MatiMcFly/DIY_ToF/docs/documentation/acronympage.tex

\section*{Abkürzungsverzeichnis}
\vspace{-25pt}
\printglossary[type=\acronymtype,title={}]

\pagebreak
