MatiMcFly/DIY_ToF/docs/presentation/english/conclusion.tex

\begin{frame}{Outlook}
    \begin{itemize}
        \item Optimize the optics, try other focal lengths
        \item Minimize jitter (higher clock or external clock)
        \item Switch GPIOs faster
        \item Optical receive path
              \begin{itemize}
                  \item Different amplifications TIA
                  \item Different switching thresholds for comparator
              \end{itemize}
        \item Optical transmission path: try higher transmission power
        \item Analysis of optical results: why two clusters?
        \item Mechanical test setup for mirror
    \end{itemize}
\end{frame}

\begin{frame}{Lessons Learned}
    \begin{itemize}
        \item Overall very satisfied
        \item Learned a lot of new things
        \item Unfortunately, a little short of time
        \item Time resolution less of a problem than the amount of light received
        \item[$\Rightarrow$] Invest more time in optics and optoelectronics
        \item[$\Rightarrow$] Easy to get an application running with a TDC7200
    \end{itemize}
\end{frame}
