MatiMcFly/DIY_ToF/docs/presentation/english/objective.tex

\begin{frame}{Setting}
    \begin{itemize}
        \item Part of a CAS -- Certificate Advanced Studies
              \begin{itemize}
                  \item CAS are post graduate studies (after bachelor/master)
                  \item CAS typically take 15 ECTS / 1 semester
                  \item Part time, e.g., Fri + Sat
              \end{itemize}
        \item<2-> CAS Sensors and Sensor Signal Conditioning \cite{ost2025casssc}
        \item<2-> As part of it: 5 week project work
    \end{itemize}
\end{frame}

\begin{frame}{Objective}
    \begin{itemize}
        \item Get familiar with TDCs (Time to Digital Converters)
              \begin{itemize}
                  \item Find out how much effort it takes to get TDC application running
              \end{itemize}
        \item<2-> Develop optical ToF demonstrator for distance measurement
              \begin{itemize}
                  \item Custom PCB with 2x TDC7200
              \end{itemize}
        \item<3-> First step: Electrical measurements (cable lengths)
        \item<3-> Second step: Optical measurements
              \begin{itemize}
                  \item Distance: 10 m
                  \item Resolution: 30 cm
              \end{itemize}
        \item<4->[$\Rightarrow$] Focused on getting practical experience; not very scientific
    \end{itemize}
\end{frame}

\begin{frame}{GitHub}
    \begin{itemize}
        \item I'm trying not to get too technical
        \item Full project (HW + FW) is available on GitHub: \url{https://github.com/MatiMcFly/DIY_ToF}
        \item<2-> Documentation English: \url{https://github.com/MatiMcFly/DIY_ToF/blob/main/docs/documentation/english/documentation.pdf}
              \begin{itemize}
                  \item Automatically translated with DeepL
              \end{itemize}
        \item<2-> Original German version: \url{https://github.com/MatiMcFly/DIY_ToF/blob/main/docs/documentation/documentation.pdf}
    \end{itemize}
\end{frame}
