MatiMcFly/DIY_ToF/docs/presentation/english/realization.tex

\begin{frame}{TDC}
    \begin{itemize}
        \item TDC7200 from TI \cite{ti2025tdc7200}
              \begin{itemize}
                  \item Resolution: 55~ps
                  \item Range 1: 12~ns \dots 500~ns
                  \item Range 2: 250~ns \dots 8~ms
                  \item Digital interface: SPI
              \end{itemize}
    \end{itemize}

    \begin{columns}
        \column{0.3\textwidth}
        \begin{figure}
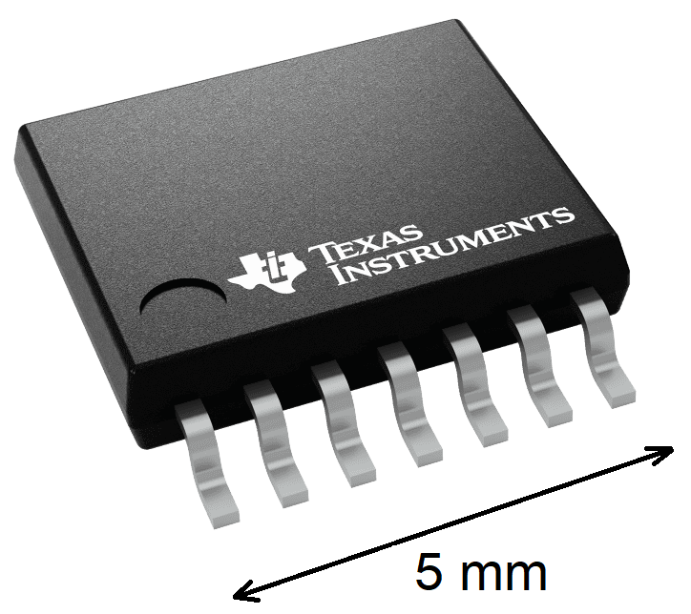
[picture p36: docs/presentation/english/graphics/tdc7200.png]
            
        \end{figure}

        \column{0.7\textwidth}
        \begin{figure}
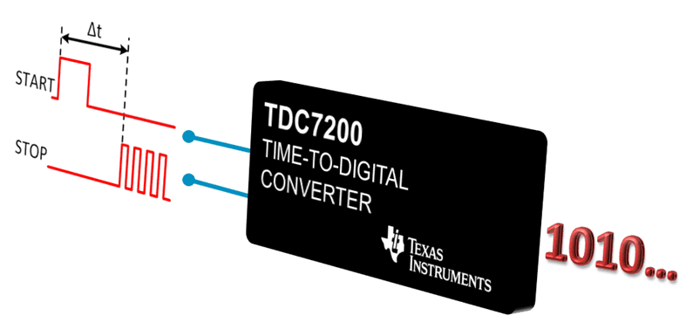
[picture p37: docs/presentation/english/graphics/tdc7200_diagram.png]
            
        \end{figure}
    \end{columns}
\end{frame}

\begin{frame}{Block diagram}
    \begin{figure}
        
    \end{figure}

    \onslide<2->{
        \begin{tikzpicture}[remember picture, overlay]
            \node at ([xshift=8.3cm, yshift=-2.6cm]current page.north west) {
                \includesvg[width=1cm]{../graphics/icon_electrical.svg}
            };
        \end{tikzpicture}

        \begin{tikzpicture}[remember picture, overlay]
            \node at ([xshift=7.9cm, yshift=-6.4cm]current page.north west) {
                \includesvg[width=1cm]{../graphics/icon_optical.svg}
            };
        \end{tikzpicture}
    }
\end{frame}

\begin{frame}{Concept: Optical Part}
    \begin{figure}
        
    \end{figure}
    \iconoptical
\end{frame}

\subsection{Circuits}

\begin{frame}{TDC Electrical}
    \begin{figure}
        
    \end{figure}
    \iconelectrical
\end{frame}

\begin{frame}{TDC Optical}
    \begin{figure}
        
    \end{figure}
    \iconoptical
\end{frame}

\begin{frame}{Laser Driver}
    \begin{figure}
        
    \end{figure}
    \iconoptical
\end{frame}

\begin{frame}{Photo Receiver}
    \begin{figure}
        
    \end{figure}
    \iconoptical
\end{frame}

\begin{frame}{3D View}
    \begin{figure}
        
    \end{figure}
\end{frame}

\begin{frame}{Demonstrator}
    \begin{figure}
        
    \end{figure}
\end{frame}

\subsection{Firmware}

\begin{frame}{Firmware block diagram}
    \begin{figure}
        
    \end{figure}
\end{frame}

\begin{frame}{Firmware example: configuration}
    \only<1>{\codehighlight{C}{1}{99}{../sourcecode/tdc_example_config.c}}
    \only<2>{\codehighlight{C}{1}{5}{../sourcecode/tdc_example_config.c}}
    \only<3>{\codehighlight{C}{7}{13}{../sourcecode/tdc_example_config.c}}
\end{frame}

\begin{frame}{Firmware example: Measurement}
    \only<1>{\codehighlight{C}{1}{99}{../sourcecode/tdc_example_measure.c}}
    \only<2>{\codehighlight{C}{4}{4}{../sourcecode/tdc_example_measure.c}}
    \only<3>{\codehighlight{C}{6}{8}{../sourcecode/tdc_example_measure.c}}
    \only<4>{\codehighlight{C}{10}{10}{../sourcecode/tdc_example_measure.c}}
    \only<5>{\codehighlight{C}{12}{12}{../sourcecode/tdc_example_measure.c}}
\end{frame}
