MatiMcFly/DIY_ToF/docs/presentation/english/tocframe.tex

\begin{frame}{Table of contents}
    \tableofcontents
\end{frame}
