MatiMcFly/DIY_ToF/docs/documentation/english/acronympage.tex

\section*{List of Acronyms}
\vspace{-25pt}
\printglossary[type=\acronymtype,title={}]

\pagebreak
