MatiMcFly/DIY_ToF/docs/documentation/english/appendix.tex

\subsection{Outline}\label{sec:outline}

\begin{figure}[H]
    \centering
    
    \caption{Outline}\label{fig:outline}
\end{figure}

\subsection{TDC Driver}\label{sec:tdc_driver}

The code in \ref{code:tdc_driver_header} and \ref{code:tdc_driver_source} shows the firmware driver developed in-house
for the \acrshort{tdc}.

\lstinputlisting[language={c}, label={code:tdc_driver_header}, caption={\acrshort{tdc} Driver (Header)}]{../../../firmware/Core/TDC/TDC.h}
\lstinputlisting[language={c}, label={code:tdc_driver_source}, caption={\acrshort{tdc} Driver (Source)}]{../../../firmware/Core/TDC/TDC.c}

\subsection{Python Scripts}\label{sec:python_scripts}

The Python script for calculating the arithmetic mean and the standard deviation, as well as for plotting the histogram
and the box plot, is shown in code \ref{code:python_analyze}.

\lstinputlisting[language={python}, label={code:python_analyze}, caption={Python Analysis}]{../../../utilities/analyze-tof.py}

The Python script for calculating the arithmetic mean and standard deviation and for plotting the values for several
\acrshort{tof} data sets is shown in code \ref{code:python_analyze_multi_tofs}.

\lstinputlisting[language={python}, label={code:python_analyze_multi_tofs}, caption={Python Analysis (Multi \acrshort{tof}s)}]{../../../utilities/analyze-tofs.py}

The Python script for plotting the values from several log files is shown in code \ref{code:python_analyze_multi_logs}.

\lstinputlisting[language={python}, label={code:python_analyze_multi_logs}, caption={Python Analysis (Multi Logs)}]{../../../utilities/analyze-tofs-multi-logs.py}

The Python script for live plotting of \acrshort{tof} values is shown in code \ref{code:python_live_plot}. This will be
used during the presentation for demonstration purposes.

\lstinputlisting[language={python}, label={code:python_live_plot}, caption={Python Live Plot}]{../../../utilities/live-plot.py}

\pagebreak

\begin{landscape}
    \subsection{Schema}\label{sec:schematic_apdx}

    \global\pdfpageattr\expandafter{\the\pdfpageattr/Rotate 90}

    \begin{figure}[H]
        \centering
        
        \caption{Schema S.1/3}\label{fig:schematics_1}
    \end{figure}
    \pagebreak

    \global\pdfpageattr\expandafter{\the\pdfpageattr/Rotate 90}

    \begin{figure}[H]
        \centering
        
        \caption{Schema S.2/3}\label{fig:schematics_2}
    \end{figure}
    \pagebreak

    \global\pdfpageattr\expandafter{\the\pdfpageattr/Rotate 90}

    \begin{figure}[H]
        \centering
        
        \caption{Schema S.3/3}\label{fig:schematics_3}
    \end{figure}
    \pagebreak

    \subsection{List of Components}

    \begin{table}[H]
        \scriptsize
        \mytable
        {|l|l|l|l|l|l|}
        {\textbf{Reference} & \textbf{Value} & \textbf{Datasheet} & \textbf{Footprint} & \textbf{Qty} & \textbf{DNP}}
        {\Reference & \Value & \Datasheet & \Footprint & \Qty & \DNP}
        {../tables/bom.csv}
        \caption{Bill of Material}\label{tab:bom}
    \end{table}
\end{landscape}

\global\pdfpageattr\expandafter{\the\pdfpageattr/Rotate 0}

\subsection{Layout}\label{sec:apdx_layout}

\begin{figure}[H]
    \centering
    
    \caption{PCB Layout Top}\label{fig:apdx_pcb_f_cu}
\end{figure}

\begin{figure}[H]
    \centering
    
    \caption{PCB Layout Inner 1}\label{fig:apdx_pcb_in1_cu}
\end{figure}

\begin{figure}[H]
    \centering
    
    \caption{PCB Layout Inner 2}\label{fig:apdx_pcb_in2_cu}
\end{figure}

\begin{figure}[H]
    \centering
    
    \caption{PCB Layout Bottom}\label{fig:apdx_pcb_b_cu}
\end{figure}

\subsection{Component Placement}\label{sec:apdx_placement}

\begin{figure}[H]
    \centering
    
    \caption{PCB component placement top}\label{fig:apdx_pcb_placement_1}
\end{figure}

\begin{figure}[H]
    \centering
    
    \caption{PCB component placement bottom}\label{fig:apdx_pcb_placement_2}
\end{figure}

\pagebreak

\subsection{3D View}\label{sec:apdx_3D_view}

\begin{figure}[H]
    \centering
    
    \caption{3D View Top}\label{fig:apdx_3d_top}
\end{figure}

\begin{figure}[H]
    \centering
    
    \caption{3D View Bottom}\label{fig:apdx_3d_bottom}
\end{figure}

\subsection{Photos of the demonstrator}\label{sec:apdx_photos_demonstrator}

\begin{figure}[H]
    \centering
    
    \caption{Demonstrator from above}\label{fig:apdx_photo_demonstrator_top}
\end{figure}

\begin{figure}[H]
    \centering
    
    \caption{Demonstrator from above without lens}\label{fig:apdx_photo_demonstrator_top_wo_lens}
\end{figure}

\begin{figure}[H]
    \centering
    
    \caption{Demonstrator from the front}\label{fig:apdx_photo_demonstrator_front}
\end{figure}

\begin{figure}[H]
    \centering
    
    \caption{Demonstrator from the front without lens}\label{fig:apdx_photo_demonstrator_front_wo_lens}
\end{figure}

\begin{figure}[H]
    \centering
    
    \caption{Demonstrator from below}\label{fig:apdx_photo_demonstrator_bottom}
\end{figure}
