MatiMcFly/DIY_ToF/docs/documentation/english/titlepage.tex

\thispagestyle{empty}

\textbf{}
\vspace{5mm}

\begin{flushleft}
    \textbf{\large{\vModule{} at the \vUniversity{}}}
\end{flushleft}

\begin{flushleft}
    \begin{small}
        \begin{tabular}{@{}lll}
            \\
            \textbf{Title}    &  & \textbf{\vTitle}                              \\
            \\
            \textbf{Student}  &  & \textbf{\vAuthorFirstName{} \vAuthorLastName} \\
            \\
            \textbf{Degree}   &  & \textbf{\vDegree}                             \\
            \\
            \textbf{Semester} &  & \textbf{\vSemester}                           \\
            \\
            \textbf{Lecturer} &  & \textbf{\vProfessor}                          \\
        \end{tabular}
    \end{small}
\end{flushleft}

\vspace{10mm}

% abstracts
\begin{small}
    \textbf{Abstract}

    \vAbstract{}
    \vspace{15mm}
\end{small}

% copyright
\begin{flushleft}
    \begin{small}
        \vCity, \date{\mydate\today} \\
        \textbf{\textcopyright\hspace{1mm}\vAuthorFirstName{} \vAuthorLastName, \vUniversity{}}
    \end{small}
\end{flushleft}

\mbox{}
\vfill

\pagebreak
