MatiMcFly/DIY_ToF/docs/presentation/english/titleframe.tex

{
    \setbeamertemplate{headline}{}
    \setbeamertemplate{footline}{}
    \begin{frame}
        \titlepage{}
    \end{frame}
}
\setlistspacing{1}{2ex}
