MatiMcFly/DIY_ToF/docs/documentation/attachments/simulation_laser_driver_schematic.pdf

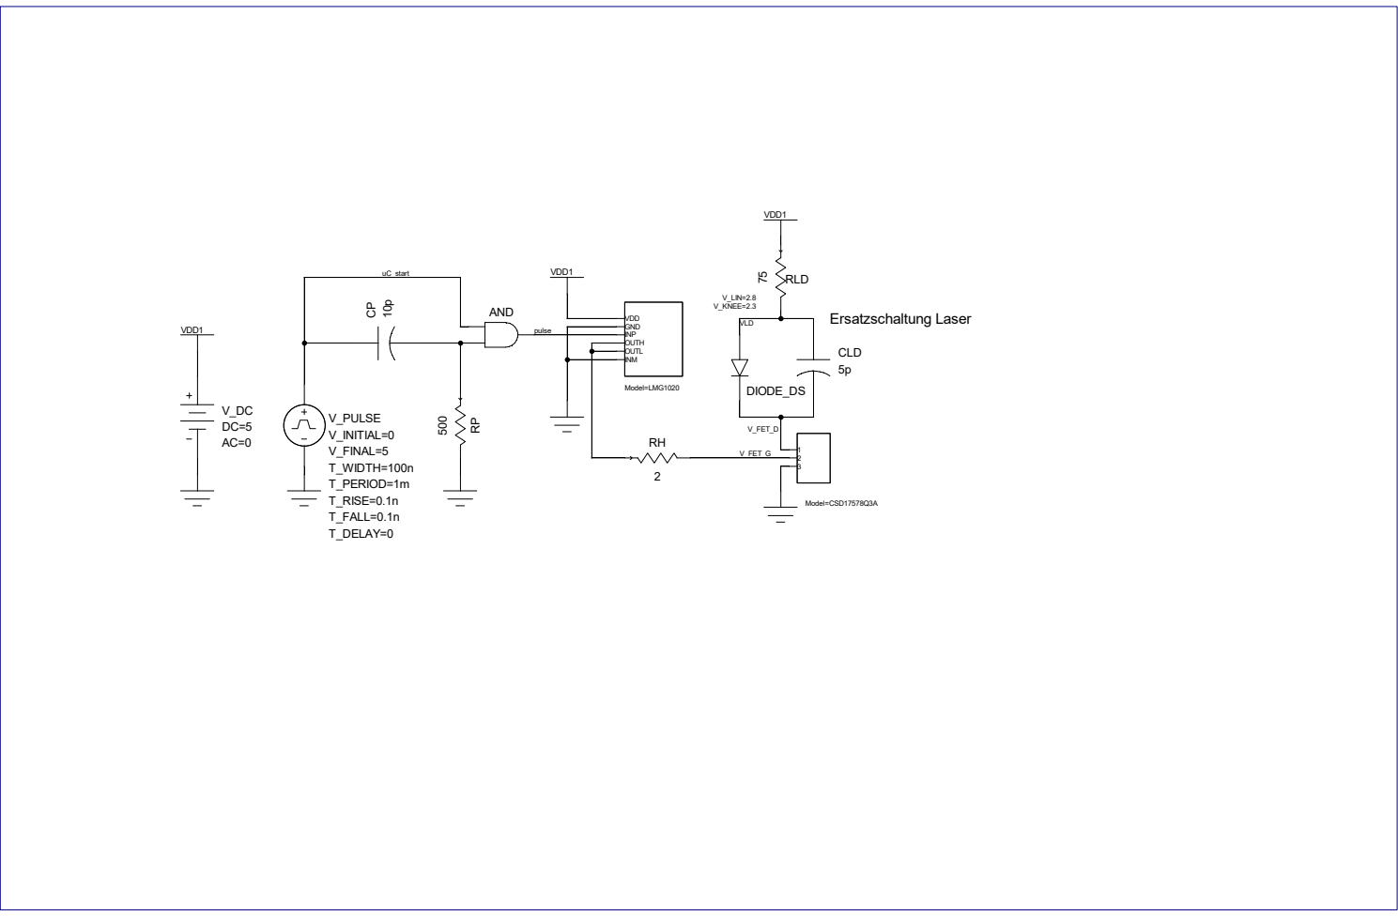
[picture p38: figure]
VDD GND INP OUTH OUTL INM; Model=LMG1020; V_FINAL=5; T_DELAY=0; V_INITIAL=0; V_PULSE; T_FALL=0.1n; T_PERIOD=1m; T_RISE=0.1n; AND; RLD; VDD1; VDD1 500 10p; T_WIDTH=100n; Ersatzschaltung Laser; DIODE_DS; CLD 5p; V_KNEE=2.3; V_LIN=2.8; uC_start; pulse; Model=CSD17578Q3A; VLD; V_FET_D; V_FET_G
