MatiMcFly/DIY_ToF/docs/presentation/document.tex

\documentclass[aspectratio=169]{beamer}

\input{settings.tex}

% Variables
\title{DIY Optische ToF Distanzmessung}
\author{Matthias Schär, Timon Burkard}
\institute{OST -- Ostschweizer Fachhochschule}
\date{24.01.2025}
\newcommand{\vModule}{CAS Sensorik und Sensor Signal Conditioning}

\begin{document}

\input{titleframe.tex}
\input{tocframe.tex}

%%%%%%%%%%%%%%%%%%%%%% CONTENT START %%%%%%%%%%%%%%%%%%%%%%

\section[Ziele]{Ziele (2 min)}
\input{ziele.tex}

\section[Umsetzung]{Umsetzung (7 min)}
\input{umsetzung.tex}

\section[Resultate]{Resultate (8 min)}
\input{resultate.tex}

\section[Fazit]{Fazit (3 min)}
\input{fazit.tex}

\section[Demonstration]{Demonstration (5 min)}
\input{demonstration.tex}

%%%%%%%%%%%%%%%%%%%%%% CONTENT END %%%%%%%%%%%%%%%%%%%%%%

\miniframesoff

\questions{}

%\input{refframe.tex}

\end{document}
