MatiMcFly/DIY_ToF/docs/documentation/einleitung.tex

In diesem Kapitel wird eine Einleitung in die Thematik der vorliegenden Projektarbeit gegeben.

Verfasst wird diese Arbeit von Timon Burkard und Matthias Schär. Betreuend stehen die Dozenten Prof. Guido Keel und
Michael Lehman zur Seite.

\subsection{Thema}

Die Arbeit befasst sich mit der Entwicklung einer Demonstrator-Elektronik für die Veranschaulichung von optischer \acrfull{tof} zur
Distanzmessung.

Es wird ein Mess-\acrshort{ic}, der TDC7200 von der Firma Texas Instruments, in Betrieb genommen. Dies geschieht in zwei
Schritten: Zuerst sollen rein elektrische Messungen ermöglicht werden, um beispielsweise die Länge von angeschlossenen
Kabeln zu bestimmen. Weiter soll sich auf dem Demonstrator die Optoelektronik befinden, welche für eine optische
Distanzmessung benötigt wird.

\subsection{Zielsetzung}

Die Studierenden haben sich zum Ziel gesetzt, eine Elektronik zu entwickeln, mit der sich die Versuche durchführen
lassen. Dabei soll die Ansteuerung der Mess-\acrshort{ic}s sowie das Auslegen der Optoelektronik ebenfalls weitgehend
selbstständig geschehen.

Es soll ein Demonstrator entstehen, mit welchem es möglich ist, unter Einsatz des TDC7200 unterschiedliche Kabellängen von
Kupferkabeln zu bestimmen. Nach dem dieses Ziel erreicht wird, soll es weiter möglich sein, optische Messungen mit dem
selben Demonstrator durchzuführen. Die Studierenden haben sich hierbei zum Ziel gesetzt, dass die Messungen mit einer Wand
als Target bis zu einer Distanz von 10~m funktionieren. Weiter sollte eine räumliche Auflösung von etwa 30~cm erreicht werden.

\subsection{Gliederung}

Nachfolgend sei ein kurzer Überblick über die Kapitel im restlichen Teil dieser Arbeit gegeben:

\begin{itemize}
    \item \textbf{Kapitel~\ref{sec:theory} - \nameref{sec:theory}:} Befasst sich mit den theoretischen Grundlagen,
          welche für die Entwicklung des Demonstrators erarbeitet wurden.

    \item \textbf{Kapitel~\ref{sec:concept} - \nameref{sec:concept}:} Erklärt die groben Konzepte und Herausforderungen,
          welche es zu bewältigen gibt. Hierbei werden insbesondere die zu entwickelnde Elektronik und die zeitlichen
          Anforderungen an den \acrshort{tdc} erfasst.

    \item \textbf{Kapitel~\ref{sec:simulations} - \nameref{sec:simulations}:} Beinhaltet Informationen zu den
          Simulationen, welche vor dem Design aber auch während der Inbetriebnahme des Demonstrators durchgeführt werden.

    \item \textbf{Kapitel~\ref{sec:realisation} - \nameref{sec:realisation}:} Erläutert die Umsetzung in die Realität.
          Hier werden Schaltungen sowie der Herstellungsprozess präsentiert. Zudem wird erklärt, was an
          Software-Entwicklung notwendig ist, um einen solchen Demonstrator zu realisieren.

    \item \textbf{Kapitel~\ref{sec:results} - \nameref{sec:results}:} Dokumentiert sämtliche durchgeführte Messungen
          sowie deren Resultate. Hier ist ersichtlich, inwiefern die initiale Zielsetzung erreicht wurde.

    \item \textbf{Kapitel~\ref{sec:conclusion} - \nameref{sec:conclusion}:} Erfasst abschliessende Gedanken der
          Studierenden und bildet ein Fazit der Arbeit. Es wird eine Aussicht auf mögliche Erweiterungen und
          Verbesserungen gegeben.
\end{itemize}
