MatiMcFly/DIY_ToF/docs/presentation/english/document.tex

\documentclass[aspectratio=169]{beamer}

\input{settings.tex}

% Variables
\title{DIY Optical ToF Distance Measurement}
\author{Matthias Schär, Timon Burkard}
\institute{OST -- Ostschweizer Fachhochschule}
\date{28.03.2025}
\newcommand{\vModule}{CAS Sensors and Sensor Signal Conditioning}

\begin{document}

\input{titleframe.tex}
\input{tocframe.tex}

%%%%%%%%%%%%%%%%%%%%%% CONTENT START %%%%%%%%%%%%%%%%%%%%%%

\section[Objective]{Objective (3 min)}
\input{objective.tex}

\section[Introduction]{Introduction (4 min)}
\input{introduction.tex}

\section[Realization]{Realization (7 min)}
\input{realization.tex}

\section[Results]{Results (8 min)}
\input{results.tex}

\section[Conclusion]{Conclusion (3 min)}
\input{conclusion.tex}

\section[Demonstration]{Demonstration (5 min)}
\input{demonstration.tex}

%%%%%%%%%%%%%%%%%%%%%% CONTENT END %%%%%%%%%%%%%%%%%%%%%%

\miniframesoff

\questions{}

\input{refframe.tex}

\end{document}
