MatiMcFly/DIY_ToF/docs/documentation/english/coverpage.tex

\title{\vspace{-40pt}\begin{huge}\textbf{\vTitle}\end{huge}\\
    \ \\ \vModule}
\author{\\\\\textbf{\vAuthorFirstName{} \vAuthorLastName}\\
    \vUniversity{}\\
    \\\\}

\date{\textcolor{red}{Translated by DeepL. Original german version: \url{https://github.com/MatiMcFly/DIY_ToF/tree/main/docs/documentation/documentation.pdf}}}
\maketitle\thispagestyle{empty}  % removes footer from first page

\vspace{20pt}

\begin{figure}[H]
    \centering
    
\end{figure}

\vspace{30pt}

\begin{figure}[H]
    \centering
    \begin{minipage}[b]{0.3\textwidth}
        \includesvg[width=\textwidth]{../graphics/OST_Logo.svg}\label{fig:OST_Logo}
    \end{minipage}
\end{figure}

\pagebreak
