MatiMcFly/DIY_ToF/docs/presentation/includes/goal.pdf

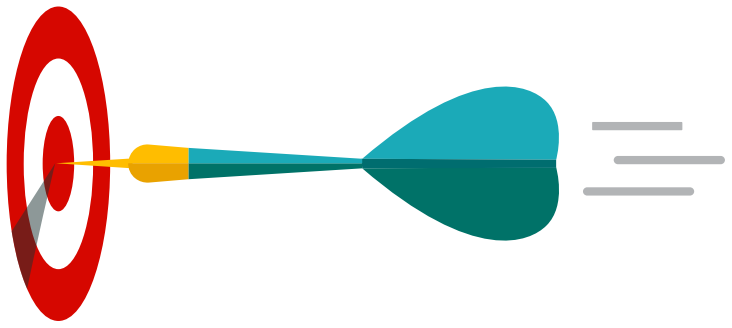
[picture p132: figure]
