MatiMcFly/DIY_ToF/docs/documentation/graphics/laser_abstrahl_charakteristik.pdf

Beam divergence

θ//
Po=7mW
| 7 | 9 | 13 | deg.

θ

⊥ | 20 | 27 | 35 | deg.
