MatiMcFly/DIY_ToF/docs/documentation/attachments/pcb_F_Cu.pdf

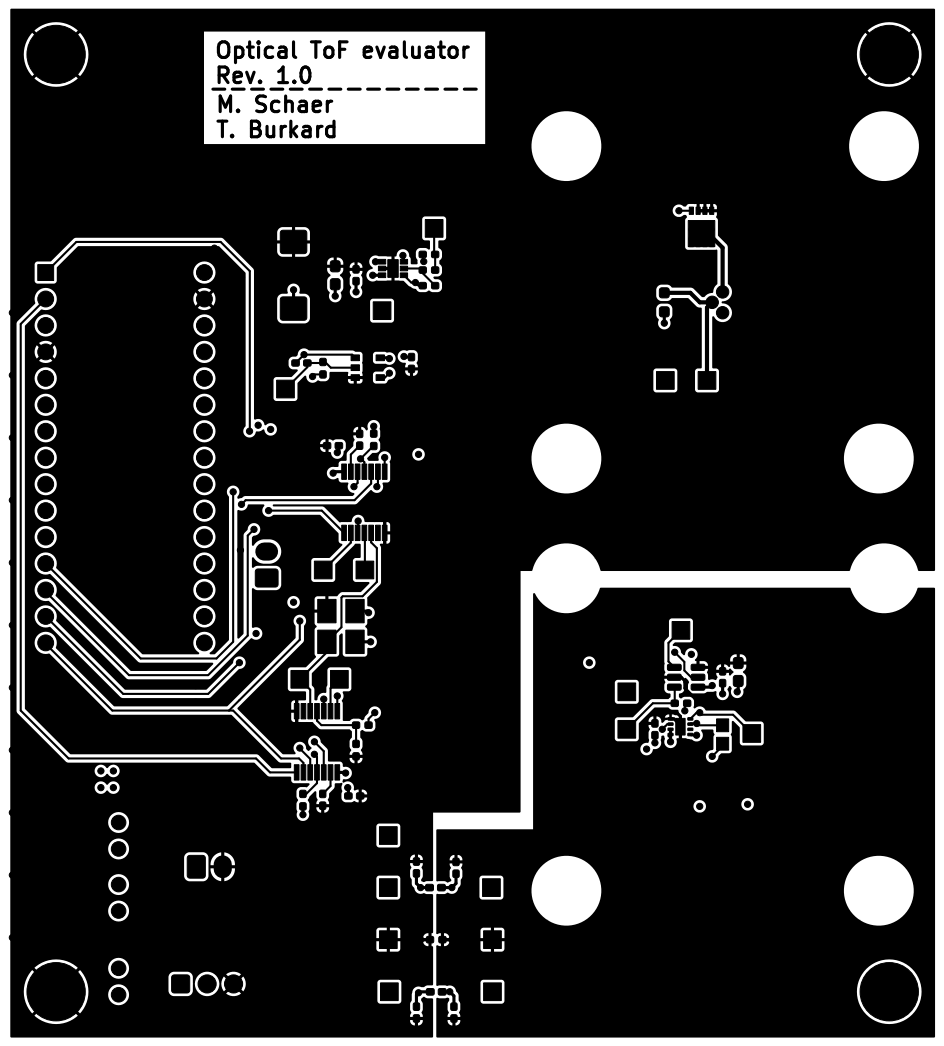
[picture p241: page 1]

Id: 1/1 Title: File: diy_tof_hw.kicad_pcb Sheet:
