MatiMcFly/DIY_ToF/docs/documentation/attachments/pcb_In2_Cu.pdf

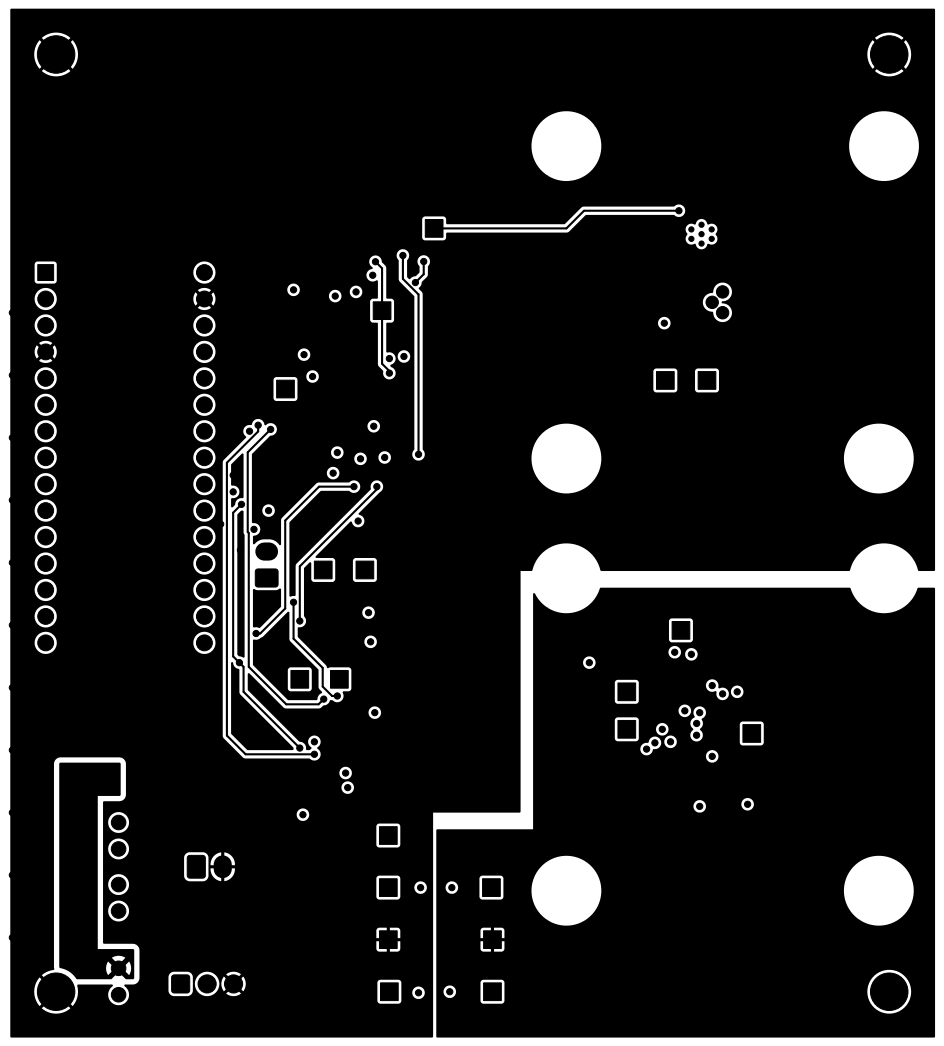
[picture p243: page 1]

Id: 1/1 Title: File: diy_tof_hw.kicad_pcb Sheet:
