MatiMcFly/DIY_ToF/docs/documentation/attachments/pcb_placement.pdf

M. Schaer T. | Burkard
-------------- Optical | ToF evaluator Rev. | 1.0

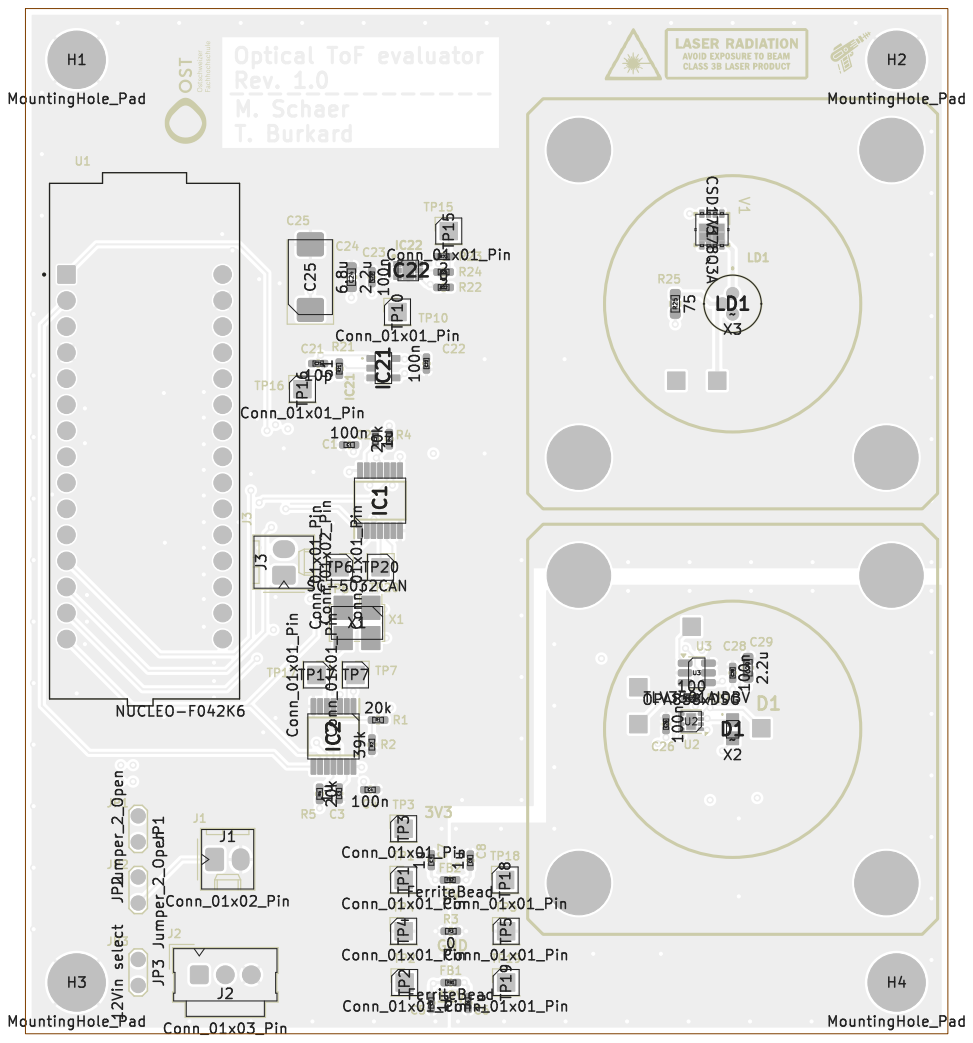
[picture p247: page 1]

RV21 1 | 2 | 3 | 4 | 5 | 6

A

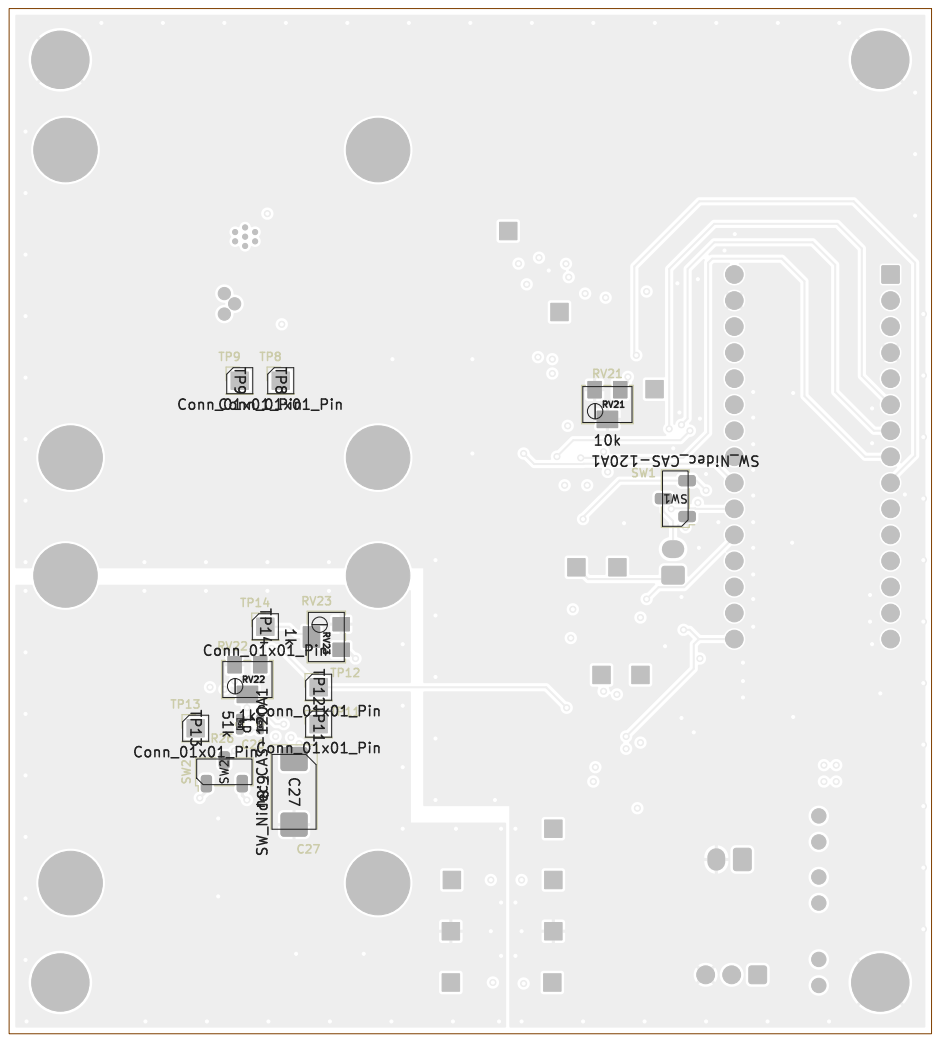
[picture p248: page 2]
