MatiMcFly/DIY_ToF/docs/documentation/sourcecode/gpio_toggle_with_hal.c

// Configure TDC

TDC_init(&tdc_ele, &hspi1, SPI_CS_ELE_GPIO_Port, SPI_CS_ELE_Pin, TDC_ELE_ENABLE_GPIO_Port, TDC_ELE_ENABLE_Pin);
TDC_enable(&tdc_ele);

TDC_read(&tdc_ele, TDC_ADR_CONFIG1, data);
data[0] |= TDC_CONFIG1_MEAS_MODE_2;

TDC_write(&tdc_ele, TDC_ADR_CONFIG1, data);

while (1) {
    TDC_start(&tdc_ele);

    // Set Pins to High with HAL
    HAL_GPIO_WritePin(START_ELE_GPIO_Port, START_ELE_Pin, GPIO_PIN_SET);
    HAL_GPIO_WritePin(STOP_ELE_GPIO_Port, STOP_ELE_Pin, GPIO_PIN_SET);

    TDC_read_result(&tdc_ele, &tof_fs);

    sprintf(string, "ToF = %lu [ps]\n", tof_fs / 1000);
    HAL_UART_Transmit(&huart2, (uint8_t *)string, strlen(string), 10000);

    // Set Pins to Low with HAL (preparation for next iteration)
    HAL_GPIO_WritePin(START_ELE_GPIO_Port, START_ELE_Pin, GPIO_PIN_RESET);
    HAL_GPIO_WritePin(STOP_ELE_GPIO_Port, STOP_ELE_Pin, GPIO_PIN_RESET);

    HAL_Delay(10); // 10 ms
}
